nurazur/TiNo/P1010040.jpg

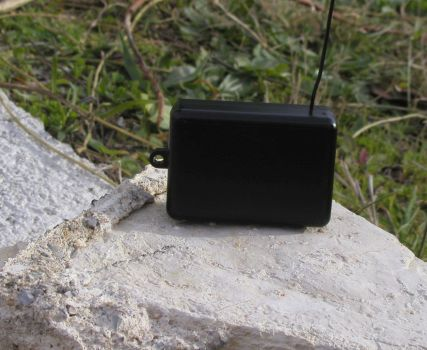
P1010040.jpg
