nurazur/TiNo/BME280_SoftwareWire/BME280b.cpp

/*
BME280.cpp
This code records data from the BME280 sensor and provides an API.
This file is part of the Arduino BME280 library.
Copyright (C) 2016   Tyler Glenn

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
Written: Dec 30 2015.
Last Updated: Oct 07 2017.

This header must be included in any derived code or copies of the code.

Based on the data sheet provided by Bosch for the Bme280 environmental sensor,
calibration code based on algorithms providedBosch, some unit conversations courtesy
of www.endmemo.com, altitude equation courtesy of NOAA, and dew point equation
courtesy of Brian McNoldy at http://andrew.rsmas.miami.edu.
 */

//#include <Wire.h>

#include "BME280b.h"


/****************************************************************/
BME280b::BME280b
(
   const Settings& settings
):m_settings(settings),
  m_initialized(false)
{
}


/****************************************************************/
bool BME280b::Initialize()
{
   bool success(true);

   success &= ReadChipID();

   if(success)
   {
      success &= ReadTrim();
      WriteSettings();
   }

   m_initialized = success;

   return m_initialized;
}

/****************************************************************/
bool BME280b::ReadChipID()
{
   uint8_t id[1];

   ReadRegister(ID_ADDR, &id[0], 1);

   if (id[0] != BME_ID && id[0] != BMP_ID)
   {
         return false;
   }

   m_chip_id = id[0];

   return true;
}


/****************************************************************/
bool BME280b::WriteSettings()
{
   uint8_t ctrlHum, ctrlMeas, config;

   CalculateRegisters(ctrlHum, ctrlMeas, config);

   WriteRegister(CTRL_HUM_ADDR, ctrlHum);
   WriteRegister(CTRL_MEAS_ADDR, ctrlMeas);
   WriteRegister(CONFIG_ADDR, config);
   return true;
}


/****************************************************************/
void BME280b::setSettings
(
   const Settings& settings
)
{
   m_settings = settings;
   WriteSettings();
}

/****************************************************************/
const BME280b::Settings& BME280b::getSettings() const
{
   return m_settings;
}


/****************************************************************/
bool BME280b::begin
(
)
{
   bool success = Initialize();
   success &= m_initialized;

   return success;
}

/****************************************************************/
void BME280b::CalculateRegisters
(
   uint8_t& ctrlHum,
   uint8_t& ctrlMeas,
   uint8_t& config
)
{
   // ctrl_hum register. (ctrl_hum[2:0] = Humidity oversampling rate.)
   ctrlHum = (uint8_t)m_settings.humOSR;
   // ctrl_meas register. (ctrl_meas[7:5] = temperature oversampling rate, ctrl_meas[4:2] = pressure oversampling rate, ctrl_meas[1:0] = mode.)
   ctrlMeas = ((uint8_t)m_settings.tempOSR << 5) | ((uint8_t)m_settings.presOSR << 2) | (uint8_t)m_settings.mode;
   // config register. (config[7:5] = standby time, config[4:2] = filter, ctrl_meas[0] = spi enable.)
   config = ((uint8_t)m_settings.standbyTime << 5) | ((uint8_t)m_settings.filter << 2) | (uint8_t)m_settings.spiEnable;
}


/****************************************************************/
bool BME280b::ReadTrim()
{
   uint8_t ord(0);
   bool success = true;

   // Temp. Dig
   success &= ReadRegister(TEMP_DIG_ADDR, &m_dig[ord], TEMP_DIG_LENGTH);
   ord += TEMP_DIG_LENGTH;

   // Pressure Dig
   success &= ReadRegister(PRESS_DIG_ADDR, &m_dig[ord], PRESS_DIG_LENGTH);
   ord += PRESS_DIG_LENGTH;

   // Humidity Dig 1
   success &= ReadRegister(HUM_DIG_ADDR1, &m_dig[ord], HUM_DIG_ADDR1_LENGTH);
   ord += HUM_DIG_ADDR1_LENGTH;

   // Humidity Dig 2
   success &= ReadRegister(HUM_DIG_ADDR2, &m_dig[ord], HUM_DIG_ADDR2_LENGTH);
   ord += HUM_DIG_ADDR2_LENGTH;

#ifdef DEBUG_ON
   Serial.print("Dig: ");
   for(int i = 0; i < 32; ++i)
   {
      Serial.print(m_dig[i], HEX);
      Serial.print(" ");
   }
   Serial.println();
#endif

   return success && ord == DIG_LENGTH;
}


/****************************************************************/
bool BME280b::ReadData
(
   int32_t data[SENSOR_DATA_LENGTH]
)
{
   bool success;
   uint8_t buffer[SENSOR_DATA_LENGTH];

   // For forced mode we need to write the mode to BME280 register before reading
   if (m_settings.mode == Mode_Forced)
   {
      WriteSettings();
   }

   // Registers are in order. So we can start at the pressure register and read 8 bytes.
   success = ReadRegister(PRESS_ADDR, buffer, SENSOR_DATA_LENGTH);

   for(int i = 0; i < SENSOR_DATA_LENGTH; ++i)
   {
      data[i] = static_cast<int32_t>(buffer[i]);
   }

#ifdef DEBUG_ON
   Serial.print("Data: ");
   for(int i = 0; i < 8; ++i)
   {
      Serial.print(data[i], HEX);
      Serial.print(" ");
   }
   Serial.println();
#endif

   return success;
}


/****************************************************************/
float BME280b::CalculateTemperature
(
   int32_t raw,
   int32_t& t_fine,
   TempUnit unit
)
{
   // Code based on calibration algorthim provided by Bosch.
   int32_t var1, var2, final;
   uint16_t dig_T1 = (m_dig[1] << 8) | m_dig[0];
   int16_t   dig_T2 = (m_dig[3] << 8) | m_dig[2];
   int16_t   dig_T3 = (m_dig[5] << 8) | m_dig[4];
   var1 = ((((raw >> 3) - ((int32_t)dig_T1 << 1))) * ((int32_t)dig_T2)) >> 11;
   var2 = (((((raw >> 4) - ((int32_t)dig_T1)) * ((raw >> 4) - ((int32_t)dig_T1))) >> 12) * ((int32_t)dig_T3)) >> 14;
   t_fine = var1 + var2;
   final = (t_fine * 5 + 128) >> 8;
   return unit == TempUnit_Celcius ? final/100.0 : final/100.0*9.0/5.0 + 32.0;
}


/****************************************************************/
float BME280b::CalculateHumidity
(
   int32_t raw,
   int32_t t_fine
)
{
   // Code based on calibration algorthim provided by Bosch.
   int32_t var1;
   uint8_t   dig_H1 =   m_dig[24];
   int16_t dig_H2 = (m_dig[26] << 8) | m_dig[25];
   uint8_t   dig_H3 =   m_dig[27];
   int16_t dig_H4 = (m_dig[28] << 4) | (0x0F & m_dig[29]);
   int16_t dig_H5 = (m_dig[30] << 4) | ((m_dig[29] >> 4) & 0x0F);
   int8_t   dig_H6 =   m_dig[31];

   var1 = (t_fine - ((int32_t)76800));
   var1 = (((((raw << 14) - (((int32_t)dig_H4) << 20) - (((int32_t)dig_H5) * var1)) +
   ((int32_t)16384)) >> 15) * (((((((var1 * ((int32_t)dig_H6)) >> 10) * (((var1 *
   ((int32_t)dig_H3)) >> 11) + ((int32_t)32768))) >> 10) + ((int32_t)2097152)) *
   ((int32_t)dig_H2) + 8192) >> 14));
   var1 = (var1 - (((((var1 >> 15) * (var1 >> 15)) >> 7) * ((int32_t)dig_H1)) >> 4));
   var1 = (var1 < 0 ? 0 : var1);
   var1 = (var1 > 419430400 ? 419430400 : var1);
   return ((uint32_t)(var1 >> 12))/1024.0;
}


/****************************************************************/
float BME280b::CalculatePressure
(
   int32_t raw,
   int32_t t_fine,
   PresUnit unit
)
{
   // Code based on calibration algorthim provided by Bosch.
   int64_t var1, var2, pressure;
   float final;

   uint16_t dig_P1 = (m_dig[7]   << 8) | m_dig[6];
   int16_t   dig_P2 = (m_dig[9]   << 8) | m_dig[8];
   int16_t   dig_P3 = (m_dig[11] << 8) | m_dig[10];
   int16_t   dig_P4 = (m_dig[13] << 8) | m_dig[12];
   int16_t   dig_P5 = (m_dig[15] << 8) | m_dig[14];
   int16_t   dig_P6 = (m_dig[17] << 8) | m_dig[16];
   int16_t   dig_P7 = (m_dig[19] << 8) | m_dig[18];
   int16_t   dig_P8 = (m_dig[21] << 8) | m_dig[20];
   int16_t   dig_P9 = (m_dig[23] << 8) | m_dig[22];

   var1 = (int64_t)t_fine - 128000;
   var2 = var1 * var1 * (int64_t)dig_P6;
   var2 = var2 + ((var1 * (int64_t)dig_P5) << 17);
   var2 = var2 + (((int64_t)dig_P4) << 35);
   var1 = ((var1 * var1 * (int64_t)dig_P3) >> 8) + ((var1 * (int64_t)dig_P2) << 12);
   var1 = (((((int64_t)1) << 47) + var1)) * ((int64_t)dig_P1) >> 33;
   if (var1 == 0) { return NAN; }                                                         // Don't divide by zero.
   pressure   = 1048576 - raw;
   pressure = (((pressure << 31) - var2) * 3125)/var1;
   var1 = (((int64_t)dig_P9) * (pressure >> 13) * (pressure >> 13)) >> 25;
   var2 = (((int64_t)dig_P8) * pressure) >> 19;
   pressure = ((pressure + var1 + var2) >> 8) + (((int64_t)dig_P7) << 4);

   final = ((uint32_t)pressure)/256.0;

   // Conversion units courtesy of www.endmemo.com.
   switch(unit){
      case PresUnit_hPa: /* hPa */
         final /= 100.0;
         break;
      case PresUnit_inHg: /* inHg */
         final /= 3386.3752577878;          /* final pa * 1inHg/3386.3752577878Pa */
         break;
      case PresUnit_atm: /* atm */
         final /= 101324.99766353; /* final pa * 1 atm/101324.99766353Pa */
         break;
      case PresUnit_bar: /* bar */
         final /= 100000.0;               /* final pa * 1 bar/100kPa */
         break;
      case PresUnit_torr: /* torr */
         final /= 133.32236534674;            /* final pa * 1 torr/133.32236534674Pa */
         break;
      case PresUnit_psi: /* psi */
         final /= 6894.744825494;   /* final pa * 1psi/6894.744825494Pa */
         break;
      default: /* Pa (case: 0) */
         break;
   }
   return final;
}


/****************************************************************/
float BME280b::temp
(
   TempUnit unit
)
{
   int32_t data[8];
   int32_t t_fine;
   if(!ReadData(data)){ return NAN; }
   uint32_t rawTemp   = (data[3] << 12) | (data[4] << 4) | (data[5] >> 4);
   return CalculateTemperature(rawTemp, t_fine, unit);
}


/****************************************************************/
float BME280b::pres
(
   PresUnit unit
)
{
   int32_t data[8];
   int32_t t_fine;
   if(!ReadData(data)){ return NAN; }
   uint32_t rawTemp       = (data[3] << 12) | (data[4] << 4) | (data[5] >> 4);
   uint32_t rawPressure = (data[0] << 12) | (data[1] << 4) | (data[2] >> 4);
   CalculateTemperature(rawTemp, t_fine);
   return CalculatePressure(rawPressure, t_fine, unit);
}


/****************************************************************/
float BME280b::hum()
{
   int32_t data[8];
   int32_t t_fine;
   if(!ReadData(data)){ return NAN; }
   uint32_t rawTemp = (data[3] << 12) | (data[4] << 4) | (data[5] >> 4);
   uint32_t rawHumidity = (data[6] << 8) | data[7];
   CalculateTemperature(rawTemp, t_fine);
   return CalculateHumidity(rawHumidity, t_fine);
}


/****************************************************************/
void BME280b::read
(
   float& pressure,
   float& temp,
   float& humidity,
   TempUnit tempUnit,
   PresUnit presUnit
)
{
   int32_t data[8];
   int32_t t_fine;
   if(!ReadData(data)){
      pressure = temp = humidity = NAN;
      return;
   }
   uint32_t rawPressure = (data[0] << 12) | (data[1] << 4) | (data[2] >> 4);
   uint32_t rawTemp = (data[3] << 12) | (data[4] << 4) | (data[5] >> 4);
   uint32_t rawHumidity = (data[6] << 8) | data[7];
   temp = CalculateTemperature(rawTemp, t_fine, tempUnit);
   pressure = CalculatePressure(rawPressure, t_fine, presUnit);
   humidity = CalculateHumidity(rawHumidity, t_fine);
}


/****************************************************************/
uint8_t BME280b::chipID
(
)
{
   return m_chip_id;
}
