nurazur/TiNo/BME280_SoftwareWire/BME280_SoftwareWire.cpp

/*
BME280I2CI2C.cpp
This code records data from the BME280I2C sensor and provides an API.
This file is part of the Arduino BME280I2C library.
Copyright (C) 2016  Tyler Glenn

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
Written: Dec 30 2015.
Last Updated: Jan 1 2016. - Happy New year!

This header must be included in any derived code or copies of the code.

Based on the data sheet provided by Bosch for the BME280I2C environmental sensor,
calibration code based on algorithms providedBosch, some unit conversations courtesy
of www.endmemo.com, altitude equation courtesy of NOAA, and dew point equation
courtesy of Brian McNoldy at http://andrew.rsmas.miami.edu.
 */


#include "BME280_SoftwareWire.h"


/****************************************************************/
BME280_SoftwareWire::BME280_SoftwareWire ( const Settings& settings)
:
  BME280b(settings),
  m_bme_280_addr(settings.bme280Addr)
{
}

/****************************************************************/
BME280_SoftwareWire::BME280_SoftwareWire ( SoftwareWire *I2C, const Settings& settings)
:
  BME280b(settings),
  m_bme_280_addr(settings.bme280Addr),
  i2c(I2C)
{
}

/****************************************************************/
bool BME280_SoftwareWire::WriteRegister
(
  uint8_t addr,
  uint8_t data
)
{
  i2c->beginTransmission(m_bme_280_addr);
  i2c->write(addr);
  i2c->write(data);
  i2c->endTransmission();

  return true; // TODO: Chech return values from wire calls.
}


/****************************************************************/
bool BME280_SoftwareWire::ReadRegister
(
  uint8_t addr,
  uint8_t data[],
  uint8_t length
)
{
  uint8_t ord(0);

  i2c->beginTransmission(m_bme_280_addr);
  i2c->write(addr);
  i2c->endTransmission();

  i2c->requestFrom(m_bme_280_addr, length);

  while(i2c->available())
  {
    data[ord++] = i2c->read();
  }

  return ord == length;
}



/****************************************************************/
float BME280_SoftwareWire::Altitude(float pressure, bool metric, float seaLevelPressure)
{
  // Equations courtesy of NOAA;
  float altitude = NAN;
  if (!isnan(pressure) && !isnan(seaLevelPressure)){
    altitude = 1000.0 * ( seaLevelPressure - pressure ) / 3386.3752577878;
  }
  return metric ? altitude * 0.3048 : altitude;
}


/****************************************************************/
float BME280_SoftwareWire::SealevelAltitude(float A, float T, float P)
{
   return(P / pow(1-((0.0065 *A) / (T + (0.0065 *A) + 273.15)),5.257));
}


/****************************************************************/
float BME280_SoftwareWire::DewPoint(float temp, float hum, bool metric)
{
  // Equations courtesy of Brian McNoldy from http://andrew.rsmas.miami.edu;
  float dewPoint = NAN;

  if (metric && !isnan(temp) && !isnan(hum))
  {
    dewPoint = 243.04 * (log(hum/100.0) + ((17.625 * temp)/(243.04 + temp)))
    /(17.625 - log(hum/100.0) - ((17.625 * temp)/(243.04 + temp)));
  }
  else if (!isnan(temp) && !isnan(hum))
  {
    float ctemp = (temp - 32.0) * 5.0/9.0;

    dewPoint = 243.04 * (log(hum/100.0) + ((17.625 * ctemp)/(243.04 + ctemp)))
    /(17.625 - log(hum/100.0) - ((17.625 * ctemp)/(243.04 + ctemp)));

    dewPoint = dewPoint * 9.0/5.0 + 32.0;
  }
  return dewPoint;
}
