nurazur/TiNo/BME280_SoftwareWire/BME280_SoftwareWire.h

/*
BME280I2C.h
This code records data from the BME280 sensor and provides an API.
This file is part of the Arduino BME280 library.
Copyright (C) 2016  Tyler Glenn

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
Written: Sep 19 2016.
Last Updated: Oct 07 2017.

This code is licensed under the GNU LGPL and is open for ditrbution
and copying in accordance with the license.
This header must be included in any derived code or copies of the code.

Based on the data sheet provided by Bosch for the Bme280 environmental sensor.
 */

#ifndef BME_280_I2C_H
#define BME_280_I2C_H

#include "BME280b.h"
#include "SoftwareWire.h"

//////////////////////////////////////////////////////////////////
/// BME280_SoftwareWire - I2C Implementation of BME280.
class BME280_SoftwareWire: public BME280b
{

public:

   struct Settings : public BME280b::Settings
   {
      Settings(
         OSR _tosr       = OSR_X1,
         OSR _hosr       = OSR_X1,
         OSR _posr       = OSR_X1,
         Mode _mode      = Mode_Forced,
         StandbyTime _st = StandbyTime_1000ms,
         Filter _filter  = Filter_Off,
         SpiEnable _se   = SpiEnable_False,
         uint8_t _addr   = 0x76
        ): BME280b::Settings(_tosr, _hosr, _posr, _mode, _st, _filter, _se),
           bme280Addr(_addr) {}

      uint8_t bme280Addr;
   };

  ///////////////////////////////////////////////////////////////
  /// Constructor used to create the class. All parameters have 
  /// default values.
  BME280_SoftwareWire( const Settings& settings = Settings() );
  BME280_SoftwareWire( SoftwareWire *i2c, const Settings& settings = Settings() );
  
  

 /////////////////////////////////////////////////////////////////
  /// Calculate the altitude based on the pressure with the
  /// specified units.
  float Altitude (float pressure, bool metric = true, float seaLevelPressure = 101325); // Pressure given in Pa.

  /////////////////////////////////////////////////////////////////
  /// Convert current pressure to sea-level pressure, returns
  /// Altitude (in meters), temperature in Celsius
  /// return the equivalent pressure at sea level.
  float SealevelAltitude( float alitude, float temp, float pres);  // A: current altitude (meters).


  /////////////////////////////////////////////////////////////////
  /// Calculate the dew point based on the temperature and
  /// humidity with the specified units.
  float DewPoint( float temp, float hum, bool metric = true);

protected:

private:

  uint8_t m_bme_280_addr;
  SoftwareWire *i2c;

  //////////////////////////////////////////////////////////////////
  /// Write values to BME280 registers.
  virtual bool WriteRegister(
    uint8_t addr,
    uint8_t data);

  /////////////////////////////////////////////////////////////////
  /// Read values from BME280 registers.
  virtual bool ReadRegister(
    uint8_t addr,
    uint8_t data[],
    uint8_t length);



  
};
  

#endif // TG_BME_280_I2C_H
