nurazur/TiNo/tools/receive_eeprom.cfg

NODEID=22
NETWORKID=210
GATEWAYID=22
VCCatCAL=3300
VCCADC_CAL=336
SENDDELAY=33
SENSORCONFIG=0x0
FREQ_CENTER=866.000000
TXPOWER=25
RADIO_T_OFFSET=0
USE_RADIO_T_COMP=0
REQUESTACK=0
LEDCOUNT=3
LEDPIN=8
LDRPIN=-1
PIRPOWERPIN=-1
PIRDEADTIME=24
RXPIN=0
TXPIN=1
SDAPIN=18
SCLPIN=19
ONEWIREDATAPIN=9
I2CPOWERPIN=9
PCI0PIN=7
PCI0TRIGGER=10
PCI0GATEWAYID=22
PCI1PIN=-1
PCI1TRIGGER=2
PCI1GATEWAYID=22
PCI2PIN=-1
PCI2TRIGGER=2
PCI2GATEWAYID=22
PCI3PIN=-1
PCI3TRIGGER=2
PCI3GATEWAYID=22
USE_CRYSTAL_RTC=0
ENCRYPTION_ENABLE=1
FEC_ENABLE=1
INTERLEAVER_ENABLE=1

TXGAUSS_SHAPING=0
SERIAL_ENABLE=1
IS_RFM69HW=1
PABOOST=0
FDEV_STEPS=0
