nurazur/TiNo/tools/tinocal_v010.py

#!/usr/bin/env python3
from __future__ import print_function
import os, sys

######### Python version ########
PY2 = (sys.version_info.major==2)
PY3 = (sys.version_info.major==3)

if os.name == 'nt':
    import msvcrt
else:
    import termios

import atexit, time

from select import select
import serial
import struct
import traceback

clipboard=False
try:
    import pyperclip
    clipboard= True
except:
    print("clipboard not found")

SerialPort = '/dev/ttyUSB_DUT'
SerialBaud = 38400
PassWord = b"TheQuickBrownFox"

##########       EEPROM MAPPING      ##########
ADR_NUM_ACTIONS = 328 # 272u + 56
ADR_ACTIONS = ADR_NUM_ACTIONS + 1
MAX_NUM_ACTIONS = 40
EEPROM_SIZE = 1024

##########      Terminal Funktions - OS dependent       #########

if os.name == 'nt': # windows OS
    # switch to normal terminal
    def set_normal_term():
        pass

    # switch to unbuffered terminal
    def set_curses_term():
        pass

    def putch(ch):
        msvcrt.putch(ch)

    def getch():
        return msvcrt.getch()

    def getche():
        return msvcrt.getche()

    def kbhit():
        return msvcrt.kbhit()

else:
    # switch to normal terminal
    def set_normal_term():
        termios.tcsetattr(fd, termios.TCSAFLUSH, old_term)

    # switch to unbuffered terminal
    def set_curses_term():
        termios.tcsetattr(fd, termios.TCSAFLUSH, new_term)

    def putch(ch):
        if PY2:
            sys.stdout.write(ch)
        elif PY3:
            if type(ch) is str:
                sys.stdout.write(ch)
            elif type(ch) is bytes:
                sys.stdout.write(ch.decode())
        sys.stdout.flush()

    def getch():
        if PY2:
            return sys.stdin.read(1)
        else:
            return sys.stdin.read(1).encode()

    def getche():
        ch = getch()
        putch(ch)
        return ch

    def kbhit():
        dr,dw,de = select([sys.stdin], [], [], 0)
        #return dr <> []  # valid in Python 2.7 not valid in Python 3
        if not dr == []:
            return True
        return False



def crc16(data):
    crc = 0xFFFF;

    if len(data) == 0:
        return 0

    for i in range(len(data)):
        #print data[i]
        dbyte = data[i]
        crc ^= (dbyte << 8)
        crc &= 0xFFFF
        for j in range(8):
            mix = crc & 0x8000
            crc = (crc << 1)
            crc &= 0xFFFF
            if (mix):
                crc = crc ^ 0x1021
            crc &= 0xFFFF
        #print ("%i, data: %i, crc: %x") % (i, data[i], crc)
    return crc;


def read_raw(port):
    raw_line=""
    if port.inWaiting() > 0:
        time.sleep(0.05)
        raw_line = port.read(port.inWaiting())
        if b'\r\n' not in raw_line[-2:]:
            done = False
            ts = time.time()
            while not done:
                if port.inWaiting() > 0:
                    raw_line += port.read(port.inWaiting())
                    if b'\r\n' in raw_line[-2:]: done = True
                else:
                    time.sleep(.01)
                if time.time() - ts > 1:
                    break;
    return raw_line


def help():
    print("'exit'          terminate program")
    print("'help'  or '?'  print this help text")
    print("'c'             measure ADC and store in EEPROM.")
    print("'copy' or 'cp'  copy file content to EEPROM. syntax: cp, <filename>")
    print("'cs'            verify checksum.")
    #print("'fe'            receive 10 packets from external source, calculate mean and store in EEPROM")
    print("'g' or 'get'    store eeprom content to file. Syntax: 'g(et),<filename>'")
    print("'la'            List definitions of actions the node shall execute")
    print("'ls'            List EEPROM content.")
    print("'m'             Measure VCC with calibrated values")
    print("'quit'          terminate program")
    print("'read'  or 'r'  read from EEPROM. Syntax: 'r(ead),<addr>'")
    print("'ri'            read 16 bit integer from EEPROM. Syntax: 'ri(ead),<addr>'")
    print("'rf'            read float from EEPROM. Syntax: 'ri(ead),<addr>'")
    print("'s'             request checksum update and store in EEPROM.")
    print("'t'             send a test RF packet ")
    print("'to'            start sending radio OOK signal")
    print("'ts'            put radio into sleep mode ")
    print("'vddcal'        calibrate VCC measurement. Syntax: 'v(ddcal),<VCC at device in mV>'")
    print("'write' or 'w'  write value to to EEPROM.  Syntax: 'w(rite),<addr>,<value>'")
    print("'wf'            write float value to EEPROM. Syntax: 'wf,<addr>,<value>'")
    print("'wl'            write long int value to to EEPROM.  Syntax: 'wl,<addr>,<value>', value format can be hex")
    print("'wu'            write unsigned int value to EEPROM. Syntax: 'wu,<addr>,<value>'")
    print("'x'             exit calibration mode and continue with loop()")


sensors = ["HTU21D", "DS18B20", "BME280", "SHT3X", "MAX31865", "BRIGHTNESS", "RESERVED"]
sensors_val =0

# copy from C++ ENUM
mem_s = "NODEIDB, NETWORKIDB, GATEWAYIDB, \
      VCCatCALi, VCCADC_CALi, \
      SENDDELAYi, \
      SENSORCONFIGB, \
      FREQ_CENTERf,\
      TXPOWERB, \
      RADIO_T_OFFSETb,\
      USE_RADIO_T_COMPB,\
      REQUESTACKB, \
      LEDCOUNTB,\
      LEDPINb,\
      LDRPINb,\
      PIRPOWERPINb,\
      PIRDEADTIMEi,\
      RXPINb,\
      TXPINb,\
      SDAPINb,\
      SCLPINb,\
      ONEWIREDATAPINb,\
      I2CPOWERPINb,\
      PCI0PINb,\
      PCI0TRIGGERB,\
      PCI0GATEWAYIDb,\
      PCI1PINb,\
      PCI1TRIGGERb,\
      PCI1GATEWAYIDb,\
      PCI2PINb,\
      PCI2TRIGGERb,\
      PCI2GATEWAYIDb,\
      PCI3PINb,\
      PCI3TRIGGERb,\
      PCI3GATEWAYIDb,\
      USE_CRYSTAL_RTCb,\
      ENCRYPTION_ENABLEb,\
      FEC_ENABLEb,\
      INTERLEAVER_ENABLEb,\
      EEPROM_VERSION_NUMBERb,\
      SOFTWAREVERSION_NUMBERi,\
      TXGAUSS_SHAPINGb,\
      SERIAL_ENABLEb,\
      IS_RFM69HWb,\
      PABOOSTb,\
      FDEV_STEPSi,\
      CHECKSUMi"


i=0
mem={} #dictionary
memtypes={}

mem_l = mem_s.split(',') # string converted to list

idx =0
for item in mem_l:
    k = item.strip()
    key = k[:-1]
    mem[key] = idx;
    mem[idx] = key;
    t = k[-1:]
    memtypes[key] = t
    memtypes[idx] = t
    if t == 'i':
        idx = idx +2
    elif t == 'f':
        idx = idx+4
    else:
        idx = idx + 1

#for index, item in enumerate(mem_l):
#    mem[item.strip()[:-1]] = index

#inv_mem = {v: k for k, v in mem.iteritems()}
#mem.update(inv_mem)

#for key in mem.keys():
#    print (key, mem[key], memtypes[key])


def write_eeprom_frequency_correction(serial):
    CEC = False
    SJK = False
    H   = False
    ALL = True
    try:
        offset = mem['CHECKSUM'] +2
        # one for all Crystals
        if ALL:
            a =   0.000104
            b =   -0.008386
            c =   0.023782
            d =   2.625568
        # SJK coefficients
        elif SJK:
            a =   0.00010445
            b = - 0.00956566
            c =   0.14759782
            d =   0.39464113

        # CEC coefficients normiert auf 23 degC
        elif CEC:
            a =   0.0000956320
            b = - 0.0079379912
            c = - 0.0013709436
            d =   3.06719812

        # -H coefficients, similar to SJK
        elif H:
            a =   0.00009504
            b = - 0.00768652
            c =   0.04871732
            d =   1.78931904
        else:
            a =   0
            b =   0
            c =   0
            d =   0

        print(a,b,c,d)
        for t in range (-30, 106):
            t2 = t * t
            t3 = t2 * t
            # coefficient formula is in ppm, but i want to write 16 bit integer values
            # so I multiply by 1000, so the coefficients are parts per billion.
            # to calculate f-steps, the driver calculates coeff * center_frequency / 61.03515625
            coeff = int(round((a*t3 + b*t2 + c*t + d) * 1000))
            if coeff > 32767:
                coeff = 32767
            #print("index: %i, memloc: %i, coeff(ppb): %i" % (t, t+30+offset, coeff))
            correction  = round(coeff * 865 / 1000 / 61.03515625)

            outstr = b"wi,%i,%i\n" % (offset, coeff)

            serial.write(outstr)
            temp = (offset - (mem['CHECKSUM'] +2))/2 -30
            print("%s, temp: %i, correction steps: %.2f" % (outstr[:-1], temp, correction))
            if SerialWaitForResponse(port):
                    read_raw(port)
            else:
                while not SerialWaitForResponse(port):
                    read_raw(port)
                    print(outstr[:-1])
                    serial.write(outstr)
                read_raw(port)

            offset += 2

    except:
        print("General ERROR when attempting to write frequency correction table")
        #print(sys.exc_info())
        print(traceback.format_exc())

#write a key value pair into configuration memory (not yet EEPROM)
# sample string looks like w,9,33 or w,SENSORCONFIG,33
def write_eeprom(str2parse, serial):
    global sensors_val
    set_sensors=False

    try:
        items = str2parse.split(b',')
        if len(items) > 2:
            thekey = items[1].decode().upper()
            if thekey in list(mem.keys()): #verbose
                addr  = mem[thekey]
            elif thekey in sensors:  # it is an item in the SENSORCONFIG bit field, thus addr is 'SENSORCONFIG'
                addr = mem['SENSORCONFIG']
                set_sensors = True
            elif '.' in thekey: # bitfield.bit, for example SENSORCONFIG.BRIGHTNESS
                bitfield = thekey.split('.')[0]
                thekey = thekey.split('.')[1]
                if thekey in sensors:
                    #addr = mem['SENSORCONFIG']
                    addr = mem[bitfield]
                    set_sensors = True
            else:
                addr = int(items[1])

            if addr in list(memtypes.keys()):
                if memtypes[addr] == 'b':  #signed char
                    if items[2][:2] == b'0x':
                        val =  int(items[2],16)
                    else:
                        val =  int(items[2]) #could be a negative number

                    if addr >= 0 and addr < EEPROM_SIZE and val >=-128 and val < 128:
                        v = ord(struct.pack('b', val))
                        outstr = b"w,%i,%i\n" % (addr, v)
                        print(outstr.decode())
                        serial.write(outstr)
                    else:
                        print("Error: incorrect value(s)")

                elif memtypes[addr] == 'B': #unsigned char
                    if items[2][:2] == b'0x':
                        val =  int(items[2],16)
                    else:
                        val =  int(items[2])

                    if set_sensors:
                        if (0 <= val) and (val <= 1):
                            i = sensors.index(thekey)
                            # set Flag at position i to 0
                            sensors_val = sensors_val & ~(1<<i)
                            sensors_val |= (val<<i)
                            outstr = b"w,%i,%i\n" % (addr, sensors_val)
                            print(outstr.decode())
                            serial.write(outstr)
                        else:
                            print("Error: bit setting can only be 0 or 1")
                            return
                    else:
                        if addr >= 0 and addr < EEPROM_SIZE and val >=0 and val < 256:
                            outstr = b"w,%i,%i\n" % (addr, val)
                            print(outstr.decode())
                            serial.write(outstr)
                        else:
                            print("Error: incorrect value(s)")

                elif memtypes[addr] == 'i': #signed 16 bit integer
                    if items[2][:2] == b'0x':
                        val =  int(items[2],16)
                    else:
                        val =  int(items[2])

                    if addr >= 0 and addr < EEPROM_SIZE-1:
                        outstr = b"wi,%i,%i\n" % (addr, val)
                        print(outstr.decode())
                        serial.write(outstr)
                    else:
                        print("Error: incorrect address value(s)")

                elif memtypes[addr] == 'f': #float
                    val =  float(items[2])
                    outstr = b"wf,%i,%f\n" % (addr, val)
                    print(outstr.decode())
                    serial.write(outstr)
                else:
                    print("wrong type")
            else:
                #print("Error: invalid address parameter")
                outstr = b"w,%s,%s" % (items[1], items[2])
                serial.write(outstr)
        else:
            print("Error: missing parameters")
    except ValueError:
        print("ERROR: probably misspelled parameter")
    except KeyError:
        print("ERROR: Parameter does not exist")
    except:
        #print("ERROR")
        #print(sys.exc_info())
        print(traceback.format_exc())


def write_eeprom_uint(str2parse, serial):
    try:
        items = str2parse.split(b',')
        if len(items) > 2:
            thekey = items[1].decode()
            if thekey in list(mem.keys()):
                addr  = mem[thekey]
            else:
                addr = int(items[1])

            if items[2][:2] == '0x':
                val =  int(items[2],16)
            else:
                val =  int(items[2])

            if addr >= 0 and addr < EEPROM_SIZE-1 and val >=0 and val < pow(2,16):
                outstr = b"w,%i,%i\n" % (addr, val&0xff) # LSB
                serial.write(outstr)
                time.sleep(.25)
                outstr = b"w,%i,%i\n" % (addr+1, val>>8) # MSB
                serial.write(outstr)
            else:
                print("Error: icorrect value(s)")
        else:
            print("Error: missing parameters")
    except:
        print(traceback.format_exc())



def write_eeprom_int16(str2parse, serial):
    try:
        items = str2parse.split(b',')
        if len(items) > 2:
            if items[1] in list(mem.keys()):
                addr  = mem[items[1]]
            else:
                addr = int(items[1])

            if items[2][:2] == '0x':
                val =  int(items[2],16)
            else:
                val =  int(items[2])

            if addr >= 0 and addr < EEPROM_SIZE-1 and val > -pow(2,15) and val < pow(2,15):
                outstr = b"wi,%i,%i\n" % (addr, val&0xFFFF)
                serial.write(outstr)
                time.sleep(.25)
            else:
                print("Error: icorrect value(s)")
        else:
            print("Error: missing parameters")
    except:
        #print("ERROR")
        #print(sys.exc_info())
        print(traceback.format_exc())

def write_eeprom_float(str2parse, serial):
    try:
        items = str2parse.split(b',')
        if len(items) > 2:
            thekey = items[1].decode()
            if thekey in list(mem.keys()):
                addr  = mem[thekey]
            else:
                addr = int(items[1])

            val =  float(items[2])

            outstr = b"wf,%i,%f\n" % (addr, val)
            print(outstr.decode())
            serial.write(outstr)

        else:
            print("Error: missing parameters")
    except:
        #print("ERROR")
        #print(sys.exc_info())
        print(traceback.format_exc())

def write_eeprom_long(str2parse, serial):
    try:
        items = str2parse.split(b',')
        if len(items) > 2:
            thekey = items[1].decode()
            if thekey in list(mem.keys()):
                addr  = mem[thekey]
            else:
                addr = int(items[1])

            if items[2][:2] == '0x':
                val =  int(items[2],16)
            else:
                val =  int(items[2])

            for i in range(4):
                outstr = b"w,%i,%i\n" % (addr+i, val & 0xff)
                val >>= 8
                serial.write(outstr)
                time.sleep(.25)
        else:
            print("Error: missing parameters")
    except:
        #print("Error")
        #print(sys.exc_info())
        print(traceback.format_exc())

def read_eeprom(str2parse, serial): #str2parse is a byte string
    try:
        items = str2parse.split(b',')
        if len(items) > 1:
            thekey = items[1].decode().upper()
            if thekey in list(mem.keys()):
                addr  = mem[thekey]
            else:
                addr = int(items[1])
            if addr >= 0 and addr < EEPROM_SIZE:
                outstr = b"r,%i\n" % (addr)
                serial.write(outstr)
            else:
                print("Error: icorrect value(s)")
        else:
            print("Error: missing parameters")
    except ValueError:
        print("ERROR - probably misspelled parameter")

    except:
        #print("ERROR")
        #print(sys.exc_info())
        print(traceback.format_exc())

def read_eeprom_float(str2parse, serial):
    try:
        items = str2parse.split(b',')
        if len(items) > 1:
            thekey = items[1].decode()
            if thekey in list(mem.keys()):
                addr  = mem[thekey]
            else:
                addr = int(items[1])
            if addr >= 0 and addr < EEPROM_SIZE-4:
                outstr = b"rf,%i\n" % (addr)
                serial.write(outstr)
            else:
                print("Error: incorrect value(s)")
        else:
            print("Error: missing parameters")
    except:
        #print("ERROR")
        #print(sys.exc_info())
        print(traceback.format_exc())


def read_eeprom_int16_t(str2parse, serial):
    try:
        items = str2parse.split(b',')
        if len(items) > 1:
            thekey = items[1].decode()
            if thekey in list(mem.keys()):
                addr  = mem[thekey]
            else:
                addr = int(items[1])
            if addr >= 0 and addr < EEPROM_SIZE-2:
                outstr = b"ri,%i\n" % (addr)
                serial.write(outstr)
            else:
                print("Error: incorrect value(s)")
        else:
            print("Error: missing parameters")
    except:
        #print "ERROR"
        #print(sys.exc_info())
        print(traceback.format_exc())

def calculate_checksum(eeprom_list):
    cs =0xaa
    for i in range(mem['CHECKSUM']):
        cs ^= int(eeprom_list[i])
    return cs & 0xff


def check_bit(value, position):
    if value & 1<<position:
        return 1
    else:
        return 0


# eepromlist is the list of raw eeprom data
# i is a particular index and must be in the dictionary
# accordingly the value is read out and a human readble Variable name as well
def parse_eeprom_list(eepromlist, i):
    global sensors_val
    outp=''
    if i in list(mem.keys()):
        #print (type(eepromlist[i]))
        t = memtypes[i]
        if t == 'b': # signed byte
            v = struct.pack('B', int(eepromlist[i])) # char[255] as a bytes array
            v = struct.unpack('b',v)[0]  # from char to signed char
            #outp = "%s=%i" %(mem[i], int(eepromlist[i]))
            outp = "%s=%i" %(mem[i], v)
            if "PCI" in mem[i] and "TRIGGER" in mem[i]:
                #print("PCI TRIGGER")
                trigger = int(eepromlist[i]) &0x3
                if trigger == 0:
                    outp = "%s #(%s, " % (outp, "LOW")
                elif trigger==1:
                    outp = "%s #(%s, " % (outp, "CHANGE")
                elif trigger==2:
                    outp = "%s #(%s, " % (outp, "FALLING")
                elif trigger==3:
                    outp = "%s #(%s, " % (outp, "RISING")
                mode = (int(eepromlist[i]) >>2) & 0x3

                if mode==0:
                    outp = "%s%s)" % (outp, "INPUT")
                elif mode==1:
                    outp = "%s%s)" % (outp, "OUTPUT")
                elif mode==2:
                    outp = "%s%s)" % (outp, "INPUT_PULLUP")
                else:
                    outp = "%s%s)" % (outp, "UNKNOWN PIN mODE")

        elif t == 'B': # unsigned Byte
            outp = "%s=%i" %(mem[i], int(eepromlist[i]))
            if "SENSORCONFIG" in mem[i]:
                sensors_val = int(eepromlist[i])
                outp = "%s=0x%X\n" % (mem[i], sensors_val)
                for p in range(len(sensors)):
                    outp += ("SENSORCONFIG.%s=%i\n" % ( sensors[p], check_bit(sensors_val, p)))

        elif t == 'i':
            if PY3:
                p= bytearray()
                p.append(int(eepromlist[i]))
                p.append(int(eepromlist[i+1]))
            else:
                p =chr(int(eepromlist[i])) + chr(int(eepromlist[i+1]))
            outp = "%s=%i" % (mem[i], struct.unpack('h', p)[0])
        elif t == 'f':
            if PY3:
                p= bytearray()
                p.append(int(eepromlist[i]))
                p.append(int(eepromlist[i+1]))
                p.append(int(eepromlist[i+2]))
                p.append(int(eepromlist[i+3]))
            else:
                p =chr(int(eepromlist[i])) + chr(int(eepromlist[i+1])) + chr(int(eepromlist[i+2])) + chr(int(eepromlist[i+3]))
            outp = "%s=%f" % (mem[i], struct.unpack('f', p)[0])
    else:
        #print("unknown parameter")
        pass
    return outp


def read_eeeprom_all(str2parse):
    eepromlist= str2parse[2:].split(b',')
    # print raw data (useful for debug only)
    #print eepromlist

    # print length of EEPROM content (useful for debug only)
    #print len(eepromlist)
    for i in range(len(eepromlist)):
        outp = parse_eeprom_list(eepromlist, i)
        if len(outp)>0:
            print(outp)



def read_actions():
    outstr = b"r,%i" % ADR_NUM_ACTIONS
    node =''
    port.write(outstr + b'\n')
    if SerialWaitForResponse(port):
        recstr = read_raw(port) # recstr is a byte string
    print ((b"Number of actions: %s" % recstr[:-2]).decode())
    numactions = int(recstr[:-2])

    port.write(b"r,0\n")
    if SerialWaitForResponse(port):
        thisnode = read_raw(port)
        #print("this node is: %s" % thisnode)


    for action in range(numactions):
        print('')
        addr = ADR_ACTIONS + action *4
        print ((b"Action %i:" % action).decode())

        outstr = b"r,%i\n" % addr
        port.write(outstr)
        if SerialWaitForResponse(port):
            node = read_raw(port)
            print((b"Node:  %s" % node[:-2]).decode())

        outstr = b"r,%i\n" % (addr+1)
        port.write(outstr)
        if SerialWaitForResponse(port):
            recstr = read_raw(port)
            print((b"Port:  %s" % recstr[:-2]).decode())

        outstr = b"r,%i\n" % (addr+2)
        port.write(outstr)
        if SerialWaitForResponse(port):
            recstr = read_raw(port)
            mask = int(recstr)
            triggersource = ''
            if node != thisnode:
                if mask & 0x1:
                    triggersource += " Heartbeat"
                if mask & 0x2:
                    triggersource += " PCI0"
                if mask & 0x4:
                    triggersource += " PCI1"
                if mask & 0x8:
                    triggersource += " PCI2"
                if mask & 0x10:
                    triggersource += " PCI3"
            else:
                if mask & 0x1:
                    triggersource += " PCI0"
                if mask & 0x2:
                    triggersource += " PCI1"
                if mask & 0x4:
                    triggersource += " PCI2"
                if mask & 0x8:
                    triggersource += " PCI3"

            print("Mask:  %s (%s )" % (recstr[:-2].decode(), triggersource))


        outstr = b"r,%i\n" % (addr+3)
        port.write(outstr)
        if SerialWaitForResponse(port):
            recstr = read_raw(port)
            pulsdur =''
            onoff = int(recstr) & 0x3
            if onoff == 0:
                mode ="OFF"
            elif onoff == 1:
                mode = "ON"
            elif onoff == 2:
                mode ="TOGGLE"
            else: #onoff == 3:
                mode = "PULSE"
                p = (int(recstr) & 0x7C)>>2
                p = pow(2,p-1)
                pulsdur = ", %.1f seconds" % p

            print("OnOff: %s (%s%s)" % (recstr[:-2].decode(), mode, pulsdur))


def eeprom2file(str2parse, filename):
    eepromlist= str2parse[2:].split(b',')
    file = open(filename, 'w')
    for i in range(len(eepromlist)):
        outp = parse_eeprom_list(eepromlist, i)
        if len(outp) > 0:
            print(outp)
            file.write(outp+'\n')
    if calculate_checksum(eepromlist) ^ int(eepromlist[mem['CHECKSUM']]) == 0:
        print("Checksum ok.")
    else:
        print("\nPython calculated Checksum: 0x%x" % calculate_checksum(eepromlist))
    file.close()

#str2parse sieht so aus: cp,<filename>
def file2eeprom(str2parse, serial):
    global sensors_val
    filepath = str2parse[3:].strip()
    if not os.path.exists(filepath):
        print ("file not found")
        return

    file = open(filepath,'r')
    content = file.readlines()
    file.close()
    set_sensors=False

    for line in content:
        set_sensors=False
        line = line.split('#',1)[0]    # remove comments from line
        items = line.split('=')
        if len(items) > 1:
            items[0] = items[0].strip()
            if items[0] in list(mem.keys()):
                addr = mem[items[0]]
            elif items[0] in sensors:  # it is an item in the SENSORCONFIG bit field, thus addr is 'SENSORCONFIG'
                addr = mem['SENSORCONFIG']
                set_sensors = True
            elif '.' in items[0]: # bitfield.bit, for example SENSORCONFIG.BRIGHTNESS
                bitfield = items[0].split('.')[0]
                items[0] = items[0].split('.')[1]
                if items[0] in sensors:
                    #addr = mem['SENSORCONFIG']
                    addr = mem[bitfield]
                    set_sensors = True
            else:
                continue

            # write Byte
            if memtypes[addr] == 'b': #signed char
                if items[1][:2] == '0x':
                    val =  int(items[1],16)
                else:
                    val =  int(items[1])
                '''
                if addr >= 0 and addr < EEPROM_SIZE and val >=-128 and val < 128:
                    v = ord(struct.pack('b', val))
                    outstr = b"w,%i,%i\n" % (addr, v)
                    print(outstr.decode())
                    serial.write(outstr)
                '''
                if addr >= 0 and addr < EEPROM_SIZE and val >=-128 and val < 128:
                    outstr = b"w,%i,%i\n" % (addr, val)
                    print(outstr[:-1].decode())
                    serial.write(outstr)
                else:
                    print("Error: incorrect value(s)")

            elif memtypes[addr] == 'B': #unsigned char
                if items[1][:2] == '0x':
                    val =  int(items[1],16)
                else:
                    val =  int(items[1])

                if set_sensors and 0 <= val and val <= 1:
                    i = sensors.index(items[0])
                    # set Flag at position i to 0
                    sensors_val = sensors_val & ~(1<<i)
                    sensors_val |= (val<<i)
                    outstr = b"w,%i,%i\n" % (addr, sensors_val)
                    print(outstr.decode())
                    serial.write(outstr)

                elif addr >= 0 and addr < EEPROM_SIZE and val >=0 and val < 256:
                    outstr = b"w,%i,%i\n" % (addr, val)
                    print(outstr[:-1].decode())
                    serial.write(outstr)
                else:
                    print("Error: incorrect value(s)")

            #write 16 bit Integer
            elif memtypes[addr] == 'i':
                if items[1][:2] == '0x':
                    val =  int(items[1],16)
                else:
                    val =  int(items[1])

                if addr >= 0 and addr < EEPROM_SIZE-1:
                    outstr = b"wi,%i,%i\n" % (addr, val)
                    print(outstr[:-1].decode())
                    serial.write(outstr)
                else:
                    print("Error: incorrect value(s)")

            #write 32 bit float
            elif memtypes[addr] == 'f':
                val =  float(items[1])
                outstr = b"wf,%i,%f\n" % (addr, val)
                print(outstr[:-1].decode())
                serial.write(outstr)
            else:
                print("wrong type")

            if SerialWaitForResponse(port):
                read_raw(port)
            else:
                while not SerialWaitForResponse(port):
                    read_raw(port)
                    print(outstr[:-1])
                    serial.write(outstr)
                read_raw(port)

    serial.write(b"s\n")
    if SerialWaitForResponse(port):
        recstr = read_raw(port)
        print("checksum: %s" % recstr.decode())

    data_arr = bytearray(MAX_NUM_ACTIONS *4) # initialized with zero's
    act_params = {'NODE':0,'PORT':1,'MASK':2,'ONOFF':3}
    number_of_actions = 0

    for line in content:
        line = line.split('#',1)[0]              # remove comments from line
        if 'ACTION' in line[:6]:                 # z.B. ACTION19.NODE = 25
            params = line.split('=')             # ['ACTION19.NODE ', ' 25']
            if len(params) >1:
                act = params[0].split('.')       # ['ACTIONS19', 'NODE ']
                act_num = int(act[0][6:])        # 19
                if len(act) > 1:
                    act_offs = act[1].rstrip()   # 'NODE'
                    if act_offs in list(act_params.keys()):
                        addr = act_num * 4 + act_params[act_offs]
                        if act_offs == 'NODE':
                            number_of_actions += 1
                    else:
                        continue # line does not contain a valid a key
                else:
                    continue # line does not contain a key
                act_val = int(params[1])
                data_arr[addr] = act_val         # put value at right place in array, because sequence is important for CRC16

                outstr = b"w,%i,%i\n" % (addr + ADR_ACTIONS, act_val)
                print(outstr[:-1].decode())
                serial.write(outstr)
                if SerialWaitForResponse(port):
                    read_raw(port)
                else:
                    while not SerialWaitForResponse(port):
                        read_raw(port)
                        print(outstr[:-1].decode())
                        serial.write(outstr)
                    read_raw(port)
            else:
                continue #line does not contain a '='

    outstr = b"w,%i,%i\n" % (ADR_NUM_ACTIONS, number_of_actions)
    print(outstr[:-1].decode())
    serial.write(outstr)  # write number of actions into EEPROM
    if SerialWaitForResponse(port):
        read_raw(port)
    data_arr[4*number_of_actions:4*MAX_NUM_ACTIONS] =[] # strip unused bytes from array

    cs = crc16(data_arr)
    cs_adr = ADR_ACTIONS + MAX_NUM_ACTIONS *4
    outstr = b"wi,%i,%i\n" %(cs_adr, cs)
    serial.write(outstr)    # write CRC16 checksum into EEPROM
    if SerialWaitForResponse(port):
        read_raw(port)
    print("checksum calculated by Python: %x" %(cs))



### calibrate VCC ###
### principle: apply a known VCC to the DUT. Let it measure VCC / raw value.
### store VCC and measured raw result in EEPROM, as VCC_CAL and ADC_CAL (2 bytes each)
### Measured VCC will be: VCC_CAL*ADC_CAL/measured result
def cal_vcc(str2parse, serial):
    try:
        items = str2parse.split(b',')
        if len(items) > 1:
            vcc = int(items[1])
            if vcc > 1800: # must be > 1.8V to operate normally.
                outstr = b"wi,%i,%i\n" % ( mem['VCCatCAL'] ,vcc)
                print(outstr[:-2].decode())
                serial.write(outstr)
                time.sleep(.25)
                serial.write(b"c\n") # request DUT to measure ADC value and store into eeprom.
            else:
                print("too small VCC! abort calibration.")
                return
        else:
            print("Error: missing parameters")
    except:
        print(" VCC calibration failed.")

def is_timeout(tstart, delayms, isset):
    if isset and ((time.time() -  tstart) > delayms/1000.0):
        return True
    else:
        return False

def OpenSerialPort(port):
    while not port.isOpen():
        try:
            port.open()
            print("ready.")
        except:
            time.sleep(0.1)

def SerialWaitForResponse(port):
    done = False
    tstart = time.time()
    while not done:
        if port.inWaiting() > 0:
            done = True
        #elif (time.time() - tstart) > 0.5:
        elif (time.time() - tstart) > 2:
            print("SerialWaitForResponse: timeout")
            return False
        time.sleep(0.01)
    return done

if __name__ == '__main__':
    argc=len(sys.argv)
    argcindex =1
    if argc > argcindex:
        if sys.argv[argcindex][0] != '-':
            SerialPort = sys.argv[argcindex]
            argcindex +=1
        if argc > argcindex:
            if sys.argv[argcindex][0] != '-':
                SerialBaud = sys.argv[argcindex]
                argcindex +=1

    if os.name != 'nt': # linux OS
        # save the terminal settings
        fd = sys.stdin.fileno()
        new_term = termios.tcgetattr(fd)
        old_term = termios.tcgetattr(fd)

        # new terminal setting unbuffered
        new_term[3] = (new_term[3] & ~termios.ICANON & ~termios.ECHO)

    atexit.register(set_normal_term)
    set_curses_term()

    inputstr=b""
    cmd_sent = ""
    storefile = ''
    recstr =b""
    tstart = time.time()
    isset_timeout = False
    timeout_delay = 500 # timeout in ms
    port  = serial.Serial()
    port.port = SerialPort
    port.baudrate = SerialBaud

    #Oeffne Seriellen Port
    OpenSerialPort(port)
    '''
    while not port.isOpen():
        try:
            port.open()
            print "ready."
        except:
            time.sleep(0.1)
    '''
    '''
    # timeout?
    if not port.isOpen():
        print "cannot connect to serial port."
        sys.exit(1)
    '''
    #sent_commands = list()
    pwd_ok = False
    while 1:
      try:
        if kbhit():
            ch = getch()

            if ord(ch) == 8 or ord(ch) == 127: #Backspace
                prompt = b'\r<-- '
                putch(b'\r')
                for i in range(len(inputstr)+4):
                    putch(b' ')
                inputstr = inputstr[:-1]

                for c in prompt:
                    if PY3:
                        c = bytes([c])
                    putch(c)
                for c in inputstr:
                    if PY3:
                        c = bytes([c])
                    putch(c)
                continue
            else:
                if inputstr ==b"":
                    inprompt = b"<-- "
                    for c in inprompt: #c is an int in PY3
                        if PY2:
                            putch(c) # this is good in PY2
                        elif PY3:
                            putch(bytes([c])) # putch wants a byte string in PY3
                putch(ch)
            if ord(ch) == 10 or ord(ch) == 13:
                print('')
                #sent_commands.append(inputstr)
                # do something with input string, i.e send over serial port
                if inputstr == b"quit" or inputstr == b"exit" or inputstr == b"q":
                    port.close()
                    break
                elif inputstr == b"help" or inputstr == b"?":
                    print("help:")
                    help()

                #write an item into EEPROM. Specify address by number or by its Name, like "write,NODEID,20'
                elif inputstr[:6] == b"write," or inputstr[:2] == b"w,":
                    write_eeprom(inputstr, port)
                    #tstart = time.time()
                    #isset_timeout = True

                #write an long int into EEPROM. Specify address by number or by its Name, like "write,NODEID,20'
                elif inputstr[:3] == b'wl,':
                    write_eeprom_long(inputstr, port)

                #write an unsigned int into EEPROM. Specify address by number or by its Name, like "write,NODEID,20'
                elif inputstr[:3] == b'wu,':
                    write_eeprom_uint(inputstr, port)

                #write an unsigned int into EEPROM. Specify address by number or by its Name, like "write,NODEID,20'
                elif inputstr[:3] == b'wi,':
                    write_eeprom_int16(inputstr, port)

                #write float value into EEPROM. Specify address by number or by its Name, like "write,NODEID,20'
                elif inputstr[:3] == b'wf,':
                    write_eeprom_float(inputstr, port)

                #read a float value from EEPROM
                elif inputstr[:3] == b"rf,":
                    read_eeprom_float(inputstr, port)

                #read a float value from EEPROM
                elif inputstr[:3] == b"ri,":
                    read_eeprom_int16_t(inputstr, port)

                #read an item from EEPROM. Specify either address by number or by its name , like "read,NODEID"
                elif inputstr[:5] == b"read," or inputstr[:2] == b"r,":
                    read_eeprom(inputstr, port)

                #calibrate VCC measurement.
                elif inputstr[:7] == b"vddcal,":
                    cal_vcc(inputstr, port)

                #request DUT to measure ADC and write result into EEPROM.
                elif inputstr == b'c':
                    port.write(b"c\n")

                #copy data from file to eeprom
                elif inputstr[:3] == b'cp,' or inputstr[:5] == b'copy,':
                    file2eeprom(inputstr, port)

                # request a list with all EEPROM items
                elif inputstr == b'a' or inputstr == b'ls':
                    port.write(b"a\n")
                    cmd_sent = inputstr # need to store this command as inputstr is reset after this loop

                # list actions definition
                elif inputstr== b'la':
                    read_actions()

                # measure FEI from a external reference signal and store in EEPROM
                # elif inputstr[:2]==b'fe':
                #    port.write(b"fe\n")

                # send a dummy packetover the air
                elif inputstr == b't':
                    print("send test packet")
                    port.write(b"t\n")

                # start the radio sending a CW signal
                elif inputstr[:2] == b'to':
                    print ("Radio CW Signal ON")
                    port.write(b"to\n")

                # put the radio to sleep
                elif inputstr[:2] == b'ts':
                    print ("Radio OFF")
                    port.write(b"ts\n")

                # request radio temp sensor reading
                elif inputstr[:2] == b'tt':
                    port.write(b"tt\n")

                # load frequency correction table into EEPROM. Values are calculated by Python from cubic parameters
                elif inputstr == b'ft' or inputstr == b'frequency_table':
                    write_eeprom_frequency_correction(port)

                # get eeprom content and save in file
                elif inputstr[:2] == b'g,' or inputstr[:4] == b'get,':
                    cmd_sent = inputstr
                    storefile = inputstr.split(b',')[1]
                    port.write(b"a\n")

                # request update of checksum
                elif inputstr == b's':
                    port.write(b"s\n")
                    tstart = time.time()
                    isset_timeout = True

                # Measure VCC with calibrated values
                elif inputstr == b'm':
                    port.write(b"m\n")

                # exit calibration mode
                elif inputstr == b'x':
                    xstr = b"x\n"
                    port.write(xstr)
                    #print "%i bytes written." % len(xstr)

                # Verify checksum
                elif inputstr == b'cs':
                    port.write(b"cs\n")

                elif inputstr ==  b'pc' or inputstr == b'close':
                    port.close()
                    print("serial port closed.")

                elif inputstr == b'po' or inputstr == b'open':
                    print("open serial port now")
                    OpenSerialPort(port)

                elif inputstr == b'pwd':
                    port.write(PassWord + b'\n')

                elif inputstr[:3] == b'pw,':
                    port.write(inputstr[3:] + b'\n')

                elif inputstr == b'v' and clipboard:  #input from Clipboard, for example: "SENDDELAY=200"
                    clpbrd = pyperclip.paste().encode()
                    print(clpbrd)
                    vv = clpbrd.split(b'=')
                    if len(vv) == 2:
                        cmd = b'w,' + vv[0] + b',' + vv[1] + b'\n'
                        #print (cmd)
                        write_eeprom(cmd, port)
                    else: #input from clipboard like "w,0,2"
                        vv = clpbrd.split(b',')
                        if len(vv)==3 and vv[0]== b'w':
                            write_eeprom(clpbrd, port)
                        else:
                            print("invalid command")

                elif len(inputstr.split(b'='))==2: #alternative input like "SENDDELAY=200"
                    vv = inputstr.split(b'=')
                    cmd = b'w,' + vv[0] + b',' + vv[1] + b'\n'
                    print (cmd)
                    write_eeprom(cmd, port)

                elif inputstr.strip().decode().upper() in mem.keys(): # just enter a parameter and get its value.
                    i= int(mem[inputstr.strip().decode().upper()])
                    if memtypes[i] =='f':
                        outp= "rf,%i\n" % i
                    elif memtypes[i] =='i':
                        outp= "ri,%i\n" % i
                    else:
                        outp= "r,%i\n" % i
                    port.write(outp.encode())

                    print ("Address: %i, type: %s, value: " %(i, memtypes[i]), end='')

                else:
                    print("Invalid command: %s" % inputstr.decode())
                    # in order to test the echo function of the device, uncomment the following 3 lines.
                    #inputstr += '\r'
                    #num = port.write(inputstr)
                    #print "Number of bytes written to serial port: %i" %(num)

                inputstr =b""
                #inprompt = "<-- "
                #for c in inprompt:
                    #putch(c)
            else:
                inputstr += ch
        if port.isOpen() and port.inWaiting() > 0:
            isset_timeout = False
            #ts = time.time()
            recstrraw = read_raw(port)           # Achtung, string returned kann \r\n enthalten == 2 Strings!
            recstrlist = recstrraw.split(b'\r\n')
            prompt = "--> "
            del recstrlist[-1]
            for recstr in recstrlist:
                if len(recstr) >  0:
                    if recstr ==b"CAL?":
                        port.write(b'y')
                        #print "received calibration request and sent 'y'"
                        #print time.time() -ts
                    elif recstr[:2] == b"a," and (cmd_sent == b'a' or cmd_sent == b'ls'):
                        #print recstr
                        read_eeeprom_all(recstr)
                    elif recstr[:2] == b"a," and (cmd_sent[:2] == b'g,' or cmd_sent[:4] == b'get,'):
                        eeprom2file(recstr, storefile)
                        storefile=''
                    elif recstr[:3] == b'cs,':
                        print("Checksum %s" % recstr[3:])
                    elif recstr[:8] == b'vcc_adc,':
                        print("VCC = %.0f mV" % float(recstr.split(b',')[1]))
                    elif recstr == b"calibration mode.":
                        print(recstr.decode())
                        # das Passwort senden wenn in der Kommandozeile als Option
                        if "-pwd" in sys.argv:
                            port.write(PassWord)
                            port.write(b'\n')
                    elif recstr == b"Pass OK":
                        pwd_ok = True
                        print(recstr.decode())
                    else:
                        #print("%s (%i bytes)" % (recstr, len(recstr)))
                        print(prompt + recstr.decode("utf-8", "ignore"))
                else:
                    print("garbage!")
            #inprompt = "<-- "
            #for c in inprompt:
                #putch(c)
        else:
            if is_timeout(tstart, timeout_delay, isset_timeout):
                isset_timeout = False
                print("timeout!!")
        # work on command line options
        if pwd_ok and argc > argcindex:
            option = sys.argv[argcindex]
            argcindex += 1
            if option =='-ls': # list EEPROM content
                cmd_sent = b'ls'
                port.write(b"a\n")
            elif option == '-cs': # query EEPROM
                print('<-- cs')
                port.write(b"cs\n")
            elif option == '-s': # update checksum
                print('<-- s')
                port.write(b"s\n")
            elif option == '-x': # store EEPROM and leave calibration mode
                port.write(b'x\n')
            elif option[:4] == '-cp,': # copy a file to EEPROM
                print(option[4:])
                file2eeprom(option[1:], port) # bloed, aber ist halt so
            elif option == '-pc': # close serial port
                port.close()
            elif option == '-q': #quit eepromer tool
                port.close()
            elif option[:7] == "-vddcal":
                cal_vcc(option[1:].encode(), port)
            elif option == '-m':
                port.write(b"m\n")
            elif option[:3]=='-w,':
                write_eeprom(option[1:], port)

        #sys.stdout.write('.')
        time.sleep(.05)
        #print '-'

      except serial.serialutil.SerialException:
        print("Serial Port Error")
        inputstr =b""
        port.close()
        #OpenSerialPort(port)
      except IOError:
        print('IO ERROR')
      except:
        #print(sys.exc_info())
        print(traceback.format_exc())


    print('done')
