nurazur/TiNo/tools/send_eeprom.cfg

NODEID=63
NETWORKID=210
GATEWAYID=22
VCCatCAL=3300
VCCADC_CAL=342
SENDDELAY=2
FREQBAND=86
FREQ_CENTER=866.000000
TXPOWER=25
REQUESTACK=0
LEDCOUNT=3
LEDPIN=8
RXPIN=0
TXPIN=1
SDAPIN=4
SCLPIN=5
I2CPOWERPIN=6
PCI0PIN=7
PCI0TRIGGER=10
PCI1PIN=128
PCI1TRIGGER=2
PCI2PIN=128
PCI2TRIGGER=10
PCI3PIN=128
PCI3TRIGGER=2
ENCRYPTION_ENABLE=1
FEC_ENABLE=1
INTERLEAVER_ENABLE=1
EEPROM_VERSION_NUMBER=4
SOFTWAREVERSION_NUMBER=7
TXGAUSS_SHAPING=0
SERIAL_ENABLE=1
IS_RFM69HW=1
PABOOST=0
FDEV_STEPS=60
CHECKSUM=138
